WROQabatya/CAESAR/3dDesignes/image/BattaryHolder.jpg

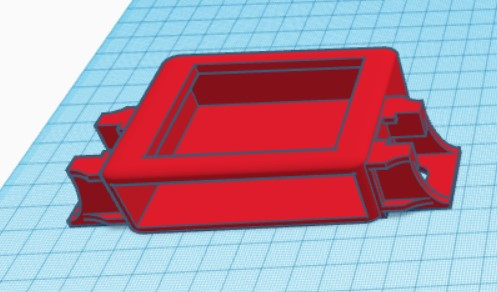
3dDesignes/image/BattaryHolder.jpg
