WROQabatya/CAESAR/3dDesignes/image/buttonAndLedMount.jpg

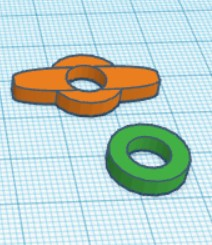
3dDesignes/image/buttonAndLedMount.jpg
