WROQabatya/CAESAR/3dDesignes/image/SensorCover.jpg

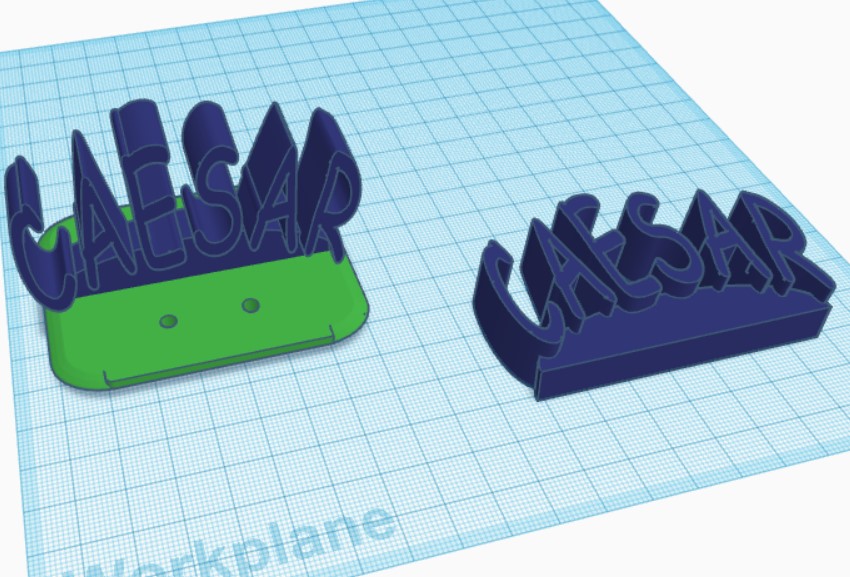
3dDesignes/image/SensorCover.jpg
