WROQabatya/CAESAR/TeemPhotos/Funny.jpeg

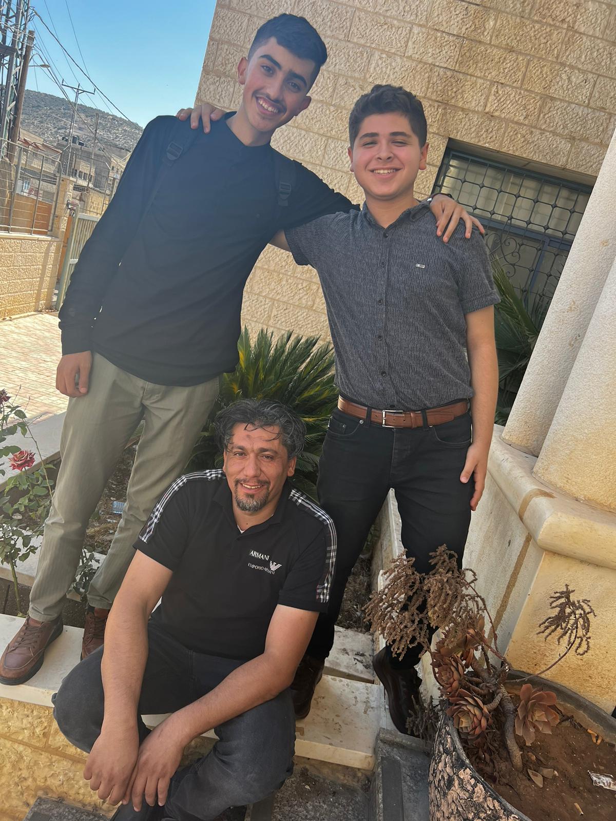
TeemPhotos/Funny.jpeg
