WROQabatya/CAESAR/TeemPhotos/official.jpeg

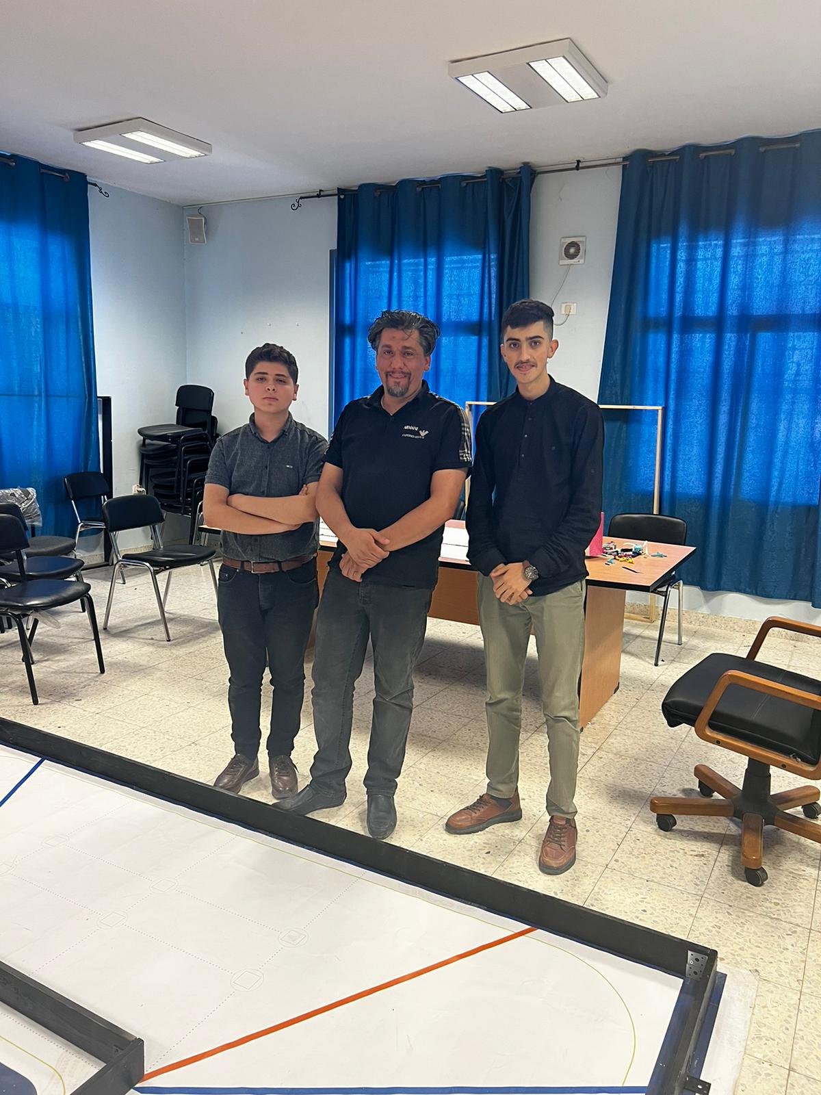
TeemPhotos/official.jpeg
