WROQabatya/CAESAR/VirticalRoboPhotos/5a0252ee-fffc-4adc-9532-27a3604911f3 (1).jpg

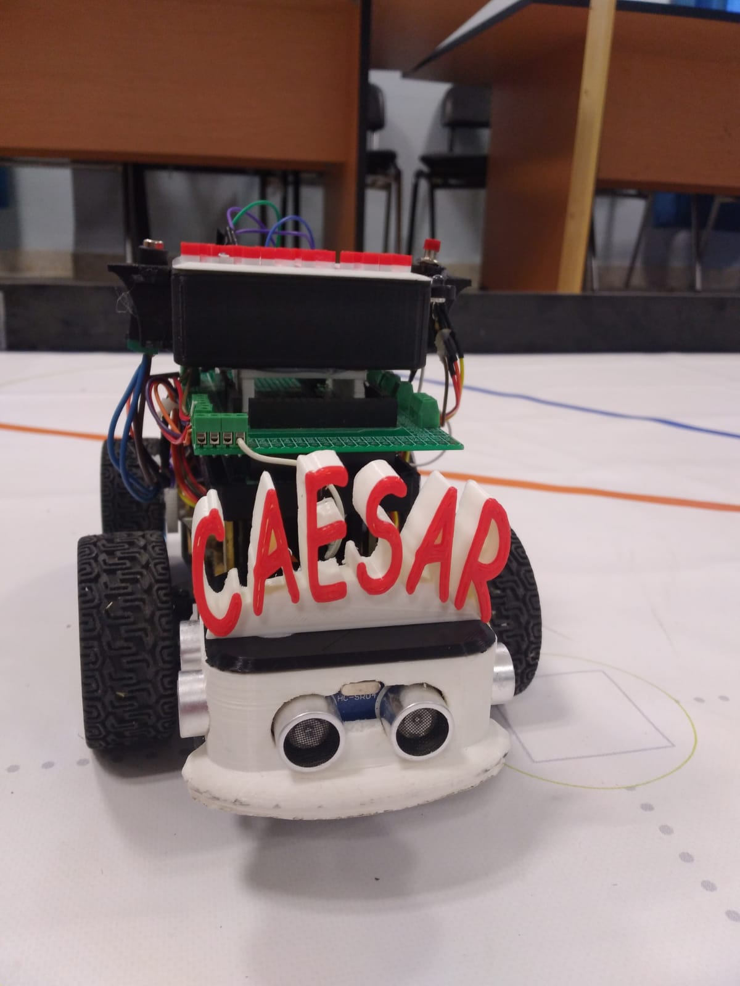
VirticalRoboPhotos/5a0252ee-fffc-4adc-9532-27a3604911f3 (1).jpg
