WROQabatya/CAESAR/VirticalRoboPhotos/1214d349-7b50-4f91-83c8-495cc8893104.jpg

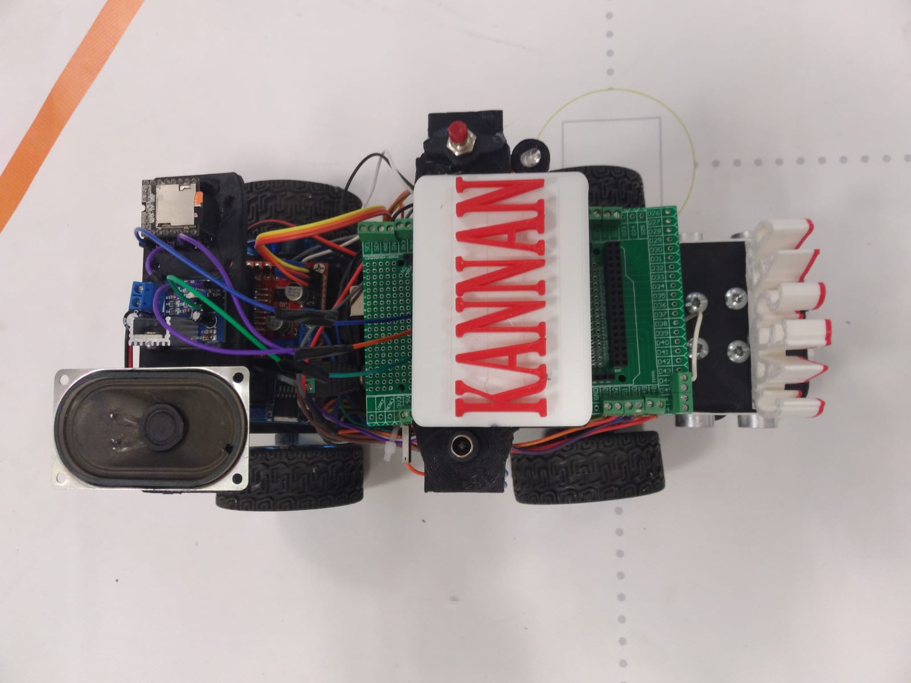
VirticalRoboPhotos/1214d349-7b50-4f91-83c8-495cc8893104.jpg
