WROQabatya/CAESAR/VirticalRoboPhotos/d8d04f3a-eb52-4d49-8ec2-71dd0b5f7c8e.jpg

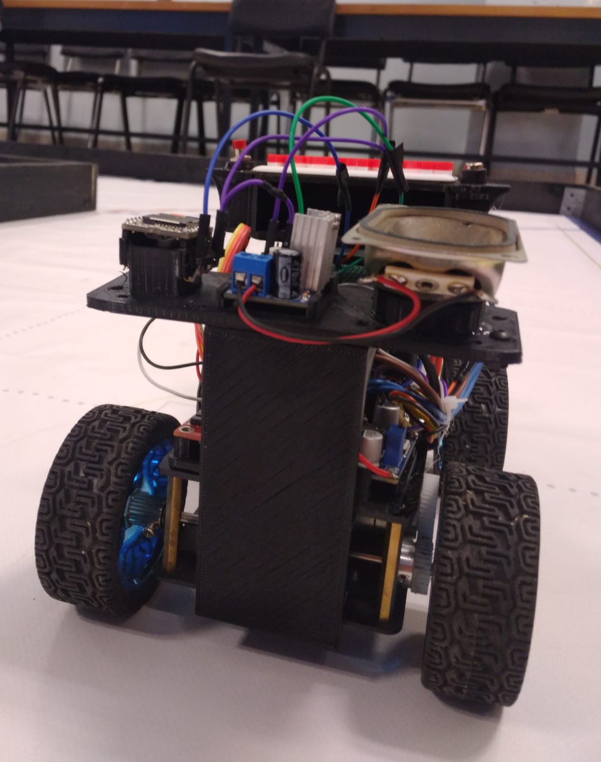
VirticalRoboPhotos/d8d04f3a-eb52-4d49-8ec2-71dd0b5f7c8e.jpg
