WROQabatya/CAESAR/VirticalRoboPhotos/fe5fbd3b-95d3-4f83-8589-3d17a7a0dce5.jpg

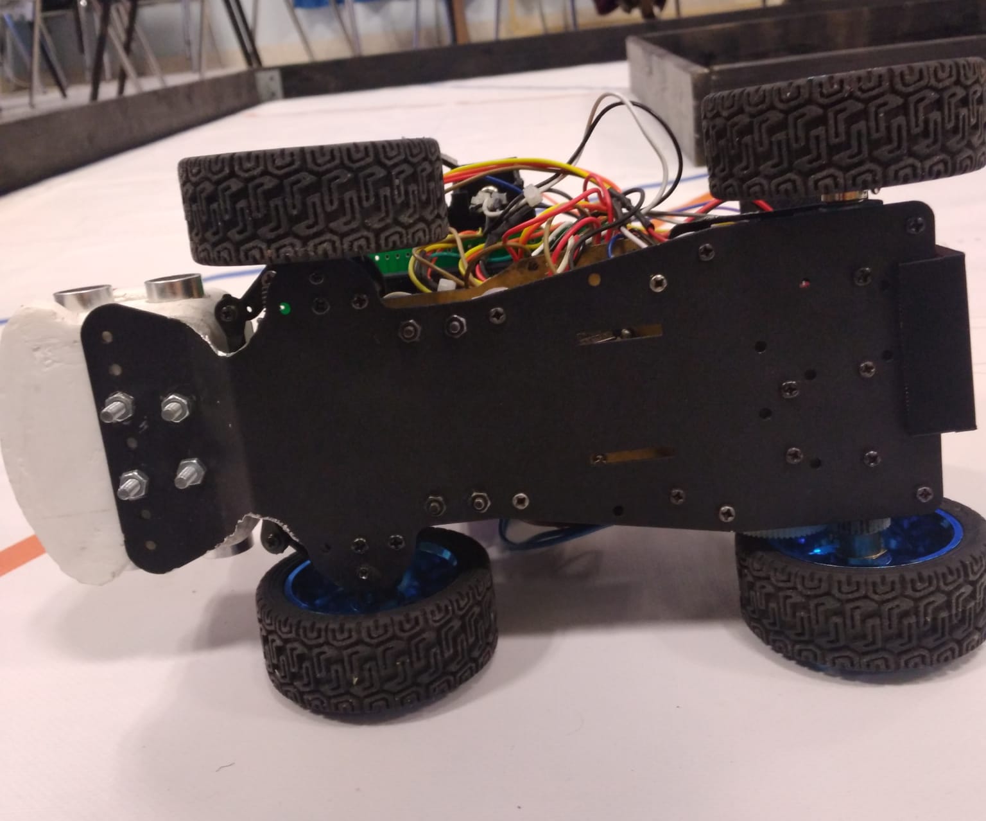
VirticalRoboPhotos/fe5fbd3b-95d3-4f83-8589-3d17a7a0dce5.jpg
